hallard/WeMos-TIC/pictures/WeMos-TIC-headers.png

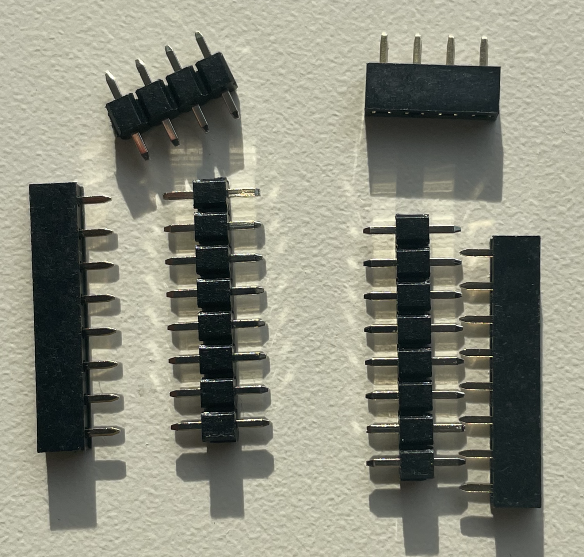
pictures/WeMos-TIC-headers.png
